fm4dd/pmod-flash/kicad/flash2.png

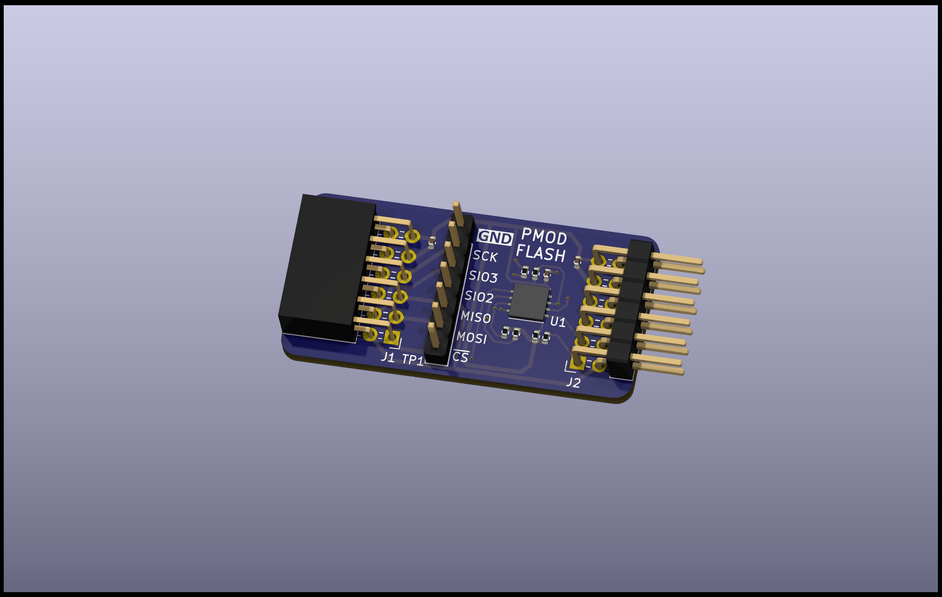
kicad/flash2.png
